CANDY-LINE/candy-pi-lite-info/cli/connection.md

<!-- toc -->

# モバイルネットワーク接続の制御

モバイルネットワーク接続の停止や再接続をコマンドラインで行うことができます。

## 接続状態表示のコマンド

現在のモバイルネットワーク接続状態を表示するには、以下のコマンドを実行してください。

```bash
$ sudo candy connection status
```

実行すると以下のような結果が表示されます。

```bash
ONLINE
```

### 結果の説明

- `ONLINE` ... モバイルネットワークに接続中です。
- `OFFLINE` ... モバイルネットワークに接続していません。

## モバイルネットワーク接続を停止する場合

現在接続している状態から切断するには、以下のコマンドを使用します。

```bash
$ sudo candy connection suspend
```

実行すると以下のような結果が表示されます。

```bash
OK
```

## モバイルネットワーク接続を再開する場合

モバイルネットワークへの接続を再開する場合は、以下のコマンドを使用します。

```bash
$ sudo candy connection resume
```

実行すると以下のような結果が表示されます。

```bash
OK
```

なお、接続を停止してから、再開するまでの間にAPNを変更したり、SIMカードを取り替えたりした場合は、モバイルネットワークへの再登録を行うため、接続までに10秒〜30秒程度かかる場合があります。

APNやSIMカードの変更を行わない場合、かつ電波状況に変化がない場合は、通常10秒未満で接続が完了します。
