CANDY-LINE/candy-pi-lite-info/upgrade/candy-pi-lite-service.md

<!-- toc -->

# candy-pi-lite サービスのバージョンアップ

candy-pi-lite サービスのバージョンアップや、インストールのやり直しを行うためには、candy-pi-lite サービスのアンインストールとインストールを行うようにしてください。

1. [candy-pi-lite サービスのアンインストール](/uninstallation/candy-pi-lite-service.md)
1. [candy-pi-lite サービスのインストール](/setup/terminal.md)
